Alexandrou4/Levitador-Magnetico/app/Sitio Web/Imagenes/Albaca.jpg

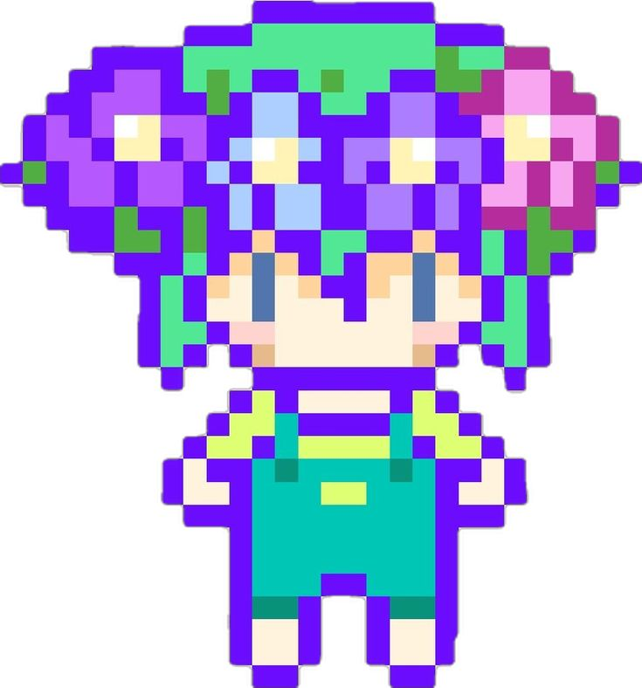
app/Sitio Web/Imagenes/Albaca.jpg
