Alexandrou4/Levitador-Magnetico/app/Sitio Web/Imagenes/santi.jpg

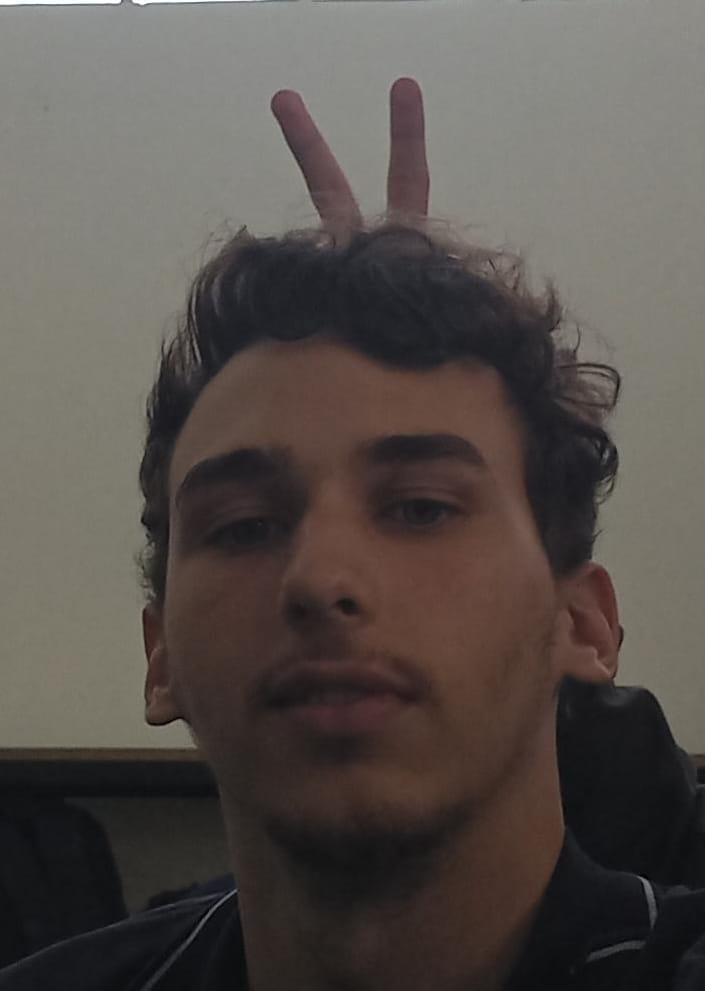
app/Sitio Web/Imagenes/santi.jpg
